Aryan-git-byte/codemate-v2/zine/assets-of-zine/render.png

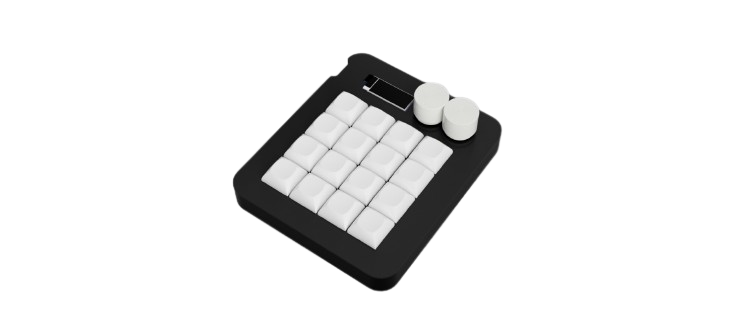
zine/assets-of-zine/render.png
