Aryan-git-byte/codemate-v2/zine/assets-of-zine/soup.png

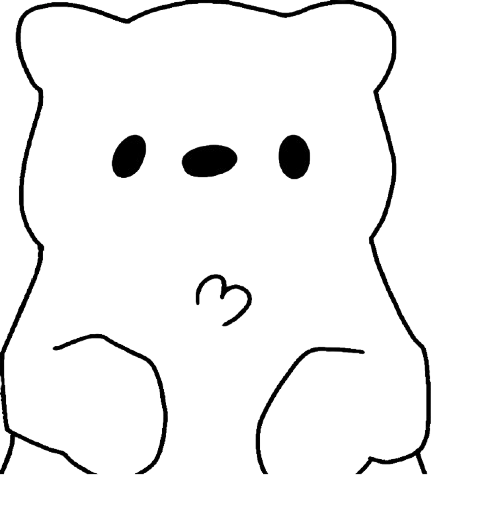
zine/assets-of-zine/soup.png
